joaocarvalhoopen/Microphone_Amplifier_for_Micro-Controller_ADC_with_LM358/kicad_microphone/microphone_for_ADC.kicad_sch

## KiCad design kicad_microphone/microphone_for_ADC.kicad_sch (2022-03-19)

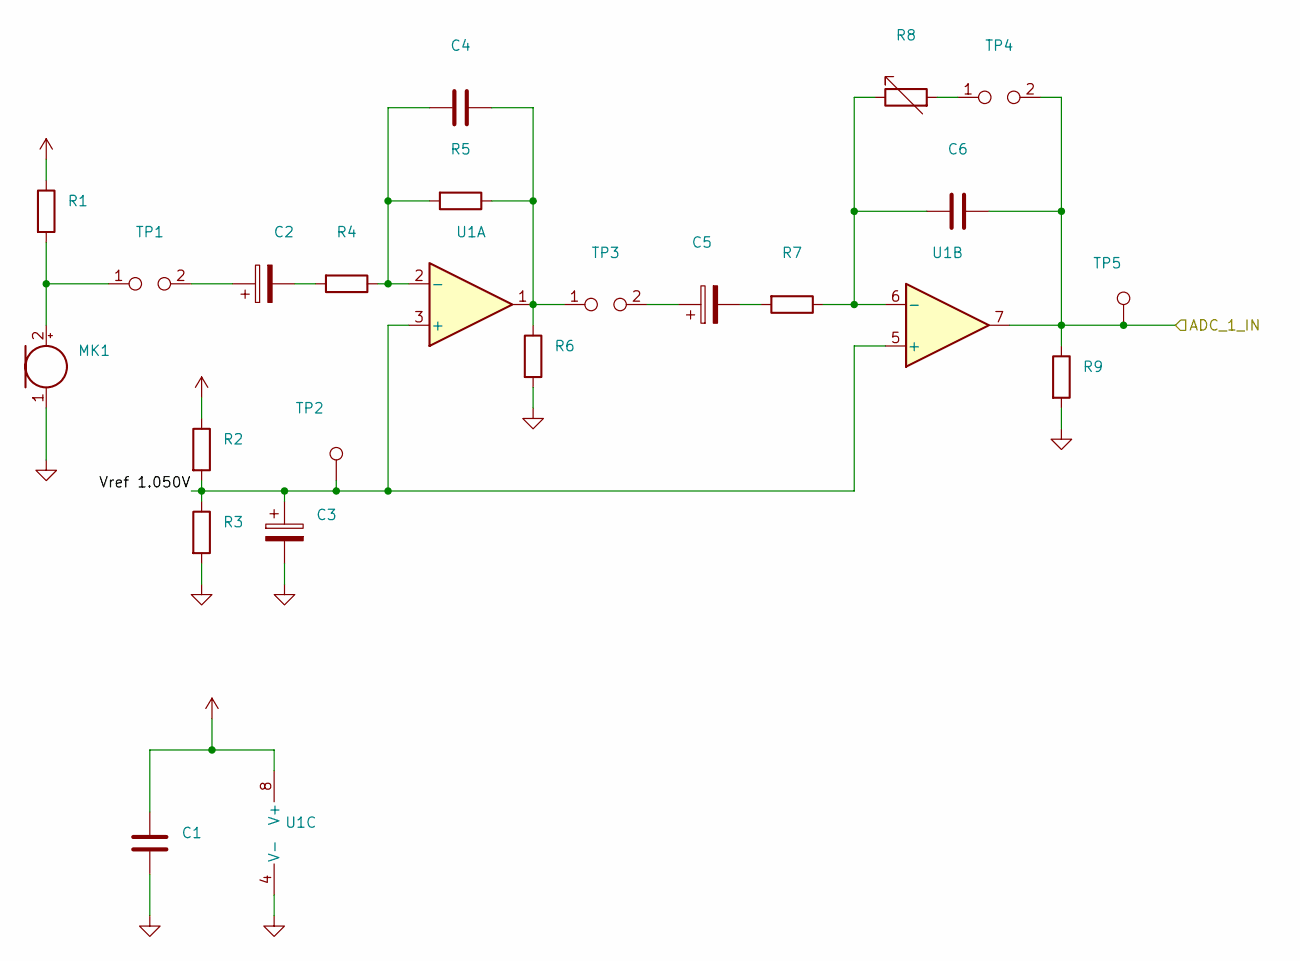
[picture p9: schematic microphone_for_ADC.kicad_sch]

Parts:
C1, C2, C3, C4, C5, C6: (no value)
MK1: (no value)
R1, R2, R3, R4, R5, R6, R7, R8, R9: (no value)
TP1, TP2, TP3, TP4, TP5: (no value)
U1: (no value)

Connections:
ADC_1_IN: C6.2, R9.1, TP4.2, TP5.1, U1.7
unnamed: C1.1, C1.2, C3.2, MK1.1 (-), R1.1, R2.1, R3.2, R6.2, R9.2, U1.4 (V-), U1.8 (V+)
unnamed: C2.1, TP1.2
unnamed: C2.2, R4.2
unnamed: C4.1, R4.1, R5.2, U1.2 (-)
unnamed: C4.2, R5.1, R6.1, TP3.1, U1.1
unnamed: C5.1, TP3.2
unnamed: C5.2, R7.2
unnamed: C6.1, R7.1, R8.1, U1.6 (-)
unnamed: MK1.2 (+), R1.2, TP1.1
unnamed: R8.2, TP4.1
Vref 1.050V: C3.1, R2.2, R3.1, TP2.1, U1.3 (+), U1.5 (+)
